GonzaloRomeroR/Teleoperation-Hexapod-Robot/Hexapod-Model/Arduino MEGA 2560 R3.jpg

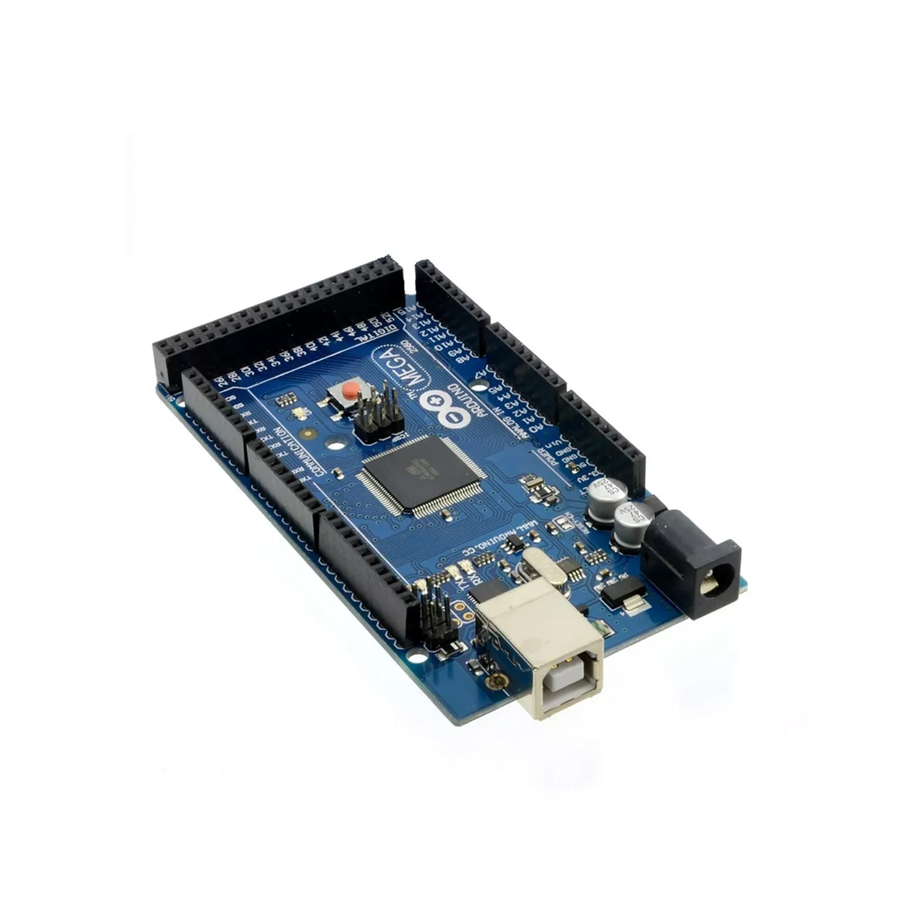
Hexapod-Model/Arduino MEGA 2560 R3.jpg
