GonzaloRomeroR/Teleoperation-Hexapod-Robot/Hexapod-Model/capture_001_10112018_191838.jpg

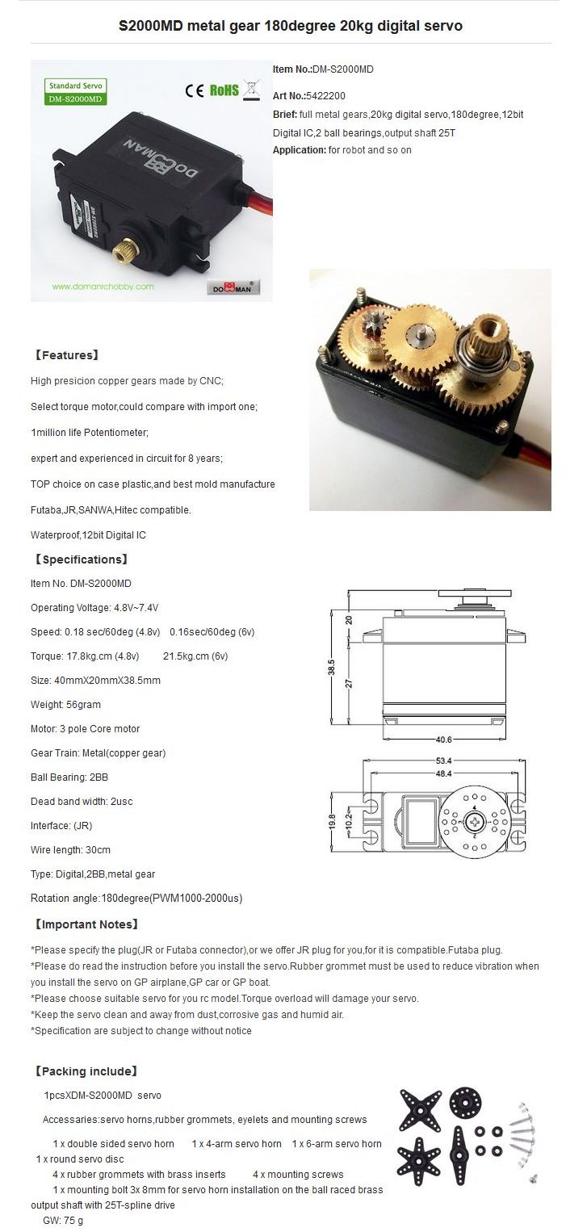
Hexapod-Model/capture_001_10112018_191838.jpg
