GonzaloRomeroR/Teleoperation-Hexapod-Robot/Hexapod-Model/DoMan Servo by Kamyar Update 1.jpg

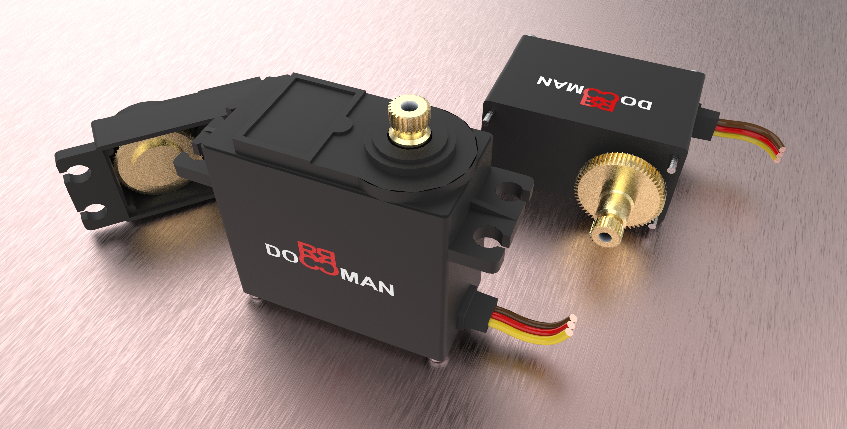
Hexapod-Model/DoMan Servo by Kamyar Update 1.jpg
