GonzaloRomeroR/Teleoperation-Hexapod-Robot/Hexapod-Model/DoMan Servo by Kamyar.jpg

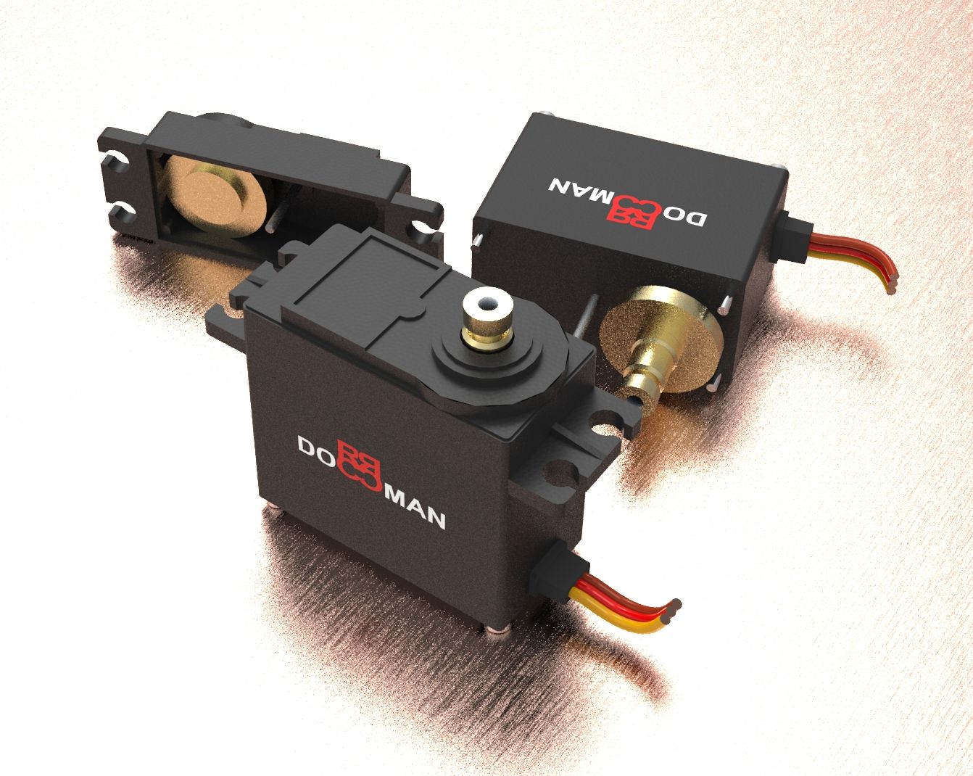
Hexapod-Model/DoMan Servo by Kamyar.jpg
