GonzaloRomeroR/Teleoperation-Hexapod-Robot/Hexapod-Model/HC-SR04.jpg

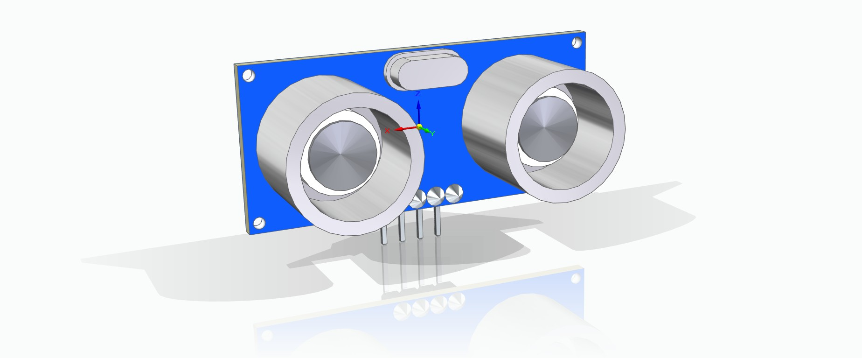
Hexapod-Model/HC-SR04.jpg
