GonzaloRomeroR/Teleoperation-Hexapod-Robot/Hexapod-Model/SensorSharpDigital/Renderings/sharp ir sensor.JPG

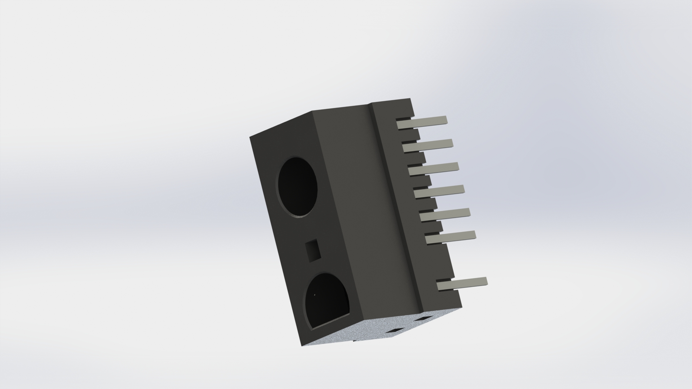
Hexapod-Model/SensorSharpDigital/Renderings/sharp ir sensor.JPG
