GonzaloRomeroR/Teleoperation-Hexapod-Robot/Hexapod-Simulation-Unity/Assets/Scripts/Joystick Pack/Sprites/All Axis Backgrounds/AllAxis_Outline.png

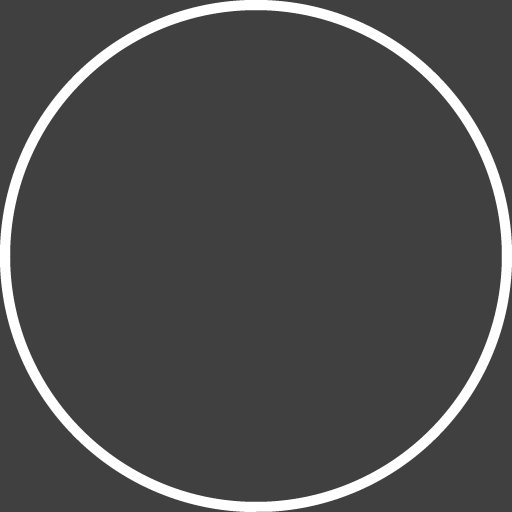
Hexapod-Simulation-Unity/Assets/Scripts/Joystick Pack/Sprites/All Axis Backgrounds/AllAxis_Outline.png
