GonzaloRomeroR/Teleoperation-Hexapod-Robot/Hexapod-Simulation-Unity/Assets/Scripts/Joystick Pack/Sprites/All Axis Backgrounds/AllAxis_Outline_Arrows.png

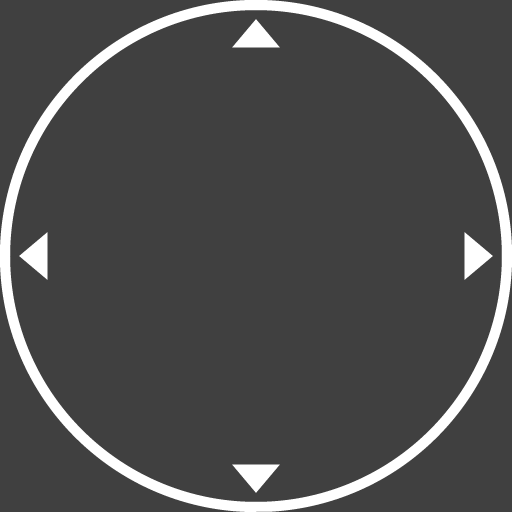
Hexapod-Simulation-Unity/Assets/Scripts/Joystick Pack/Sprites/All Axis Backgrounds/AllAxis_Outline_Arrows.png
