GonzaloRomeroR/Teleoperation-Hexapod-Robot/Hexapod-Simulation-Unity/Assets/Scripts/Joystick Pack/Sprites/All Axis Backgrounds/AllAxis_Ridged.png

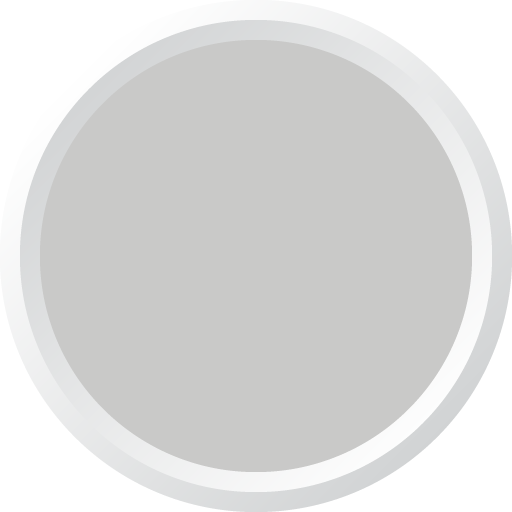
Hexapod-Simulation-Unity/Assets/Scripts/Joystick Pack/Sprites/All Axis Backgrounds/AllAxis_Ridged.png
