GonzaloRomeroR/Teleoperation-Hexapod-Robot/Hexapod-Simulation-Unity/Assets/Scripts/Joystick Pack/Sprites/All Axis Backgrounds/AllAxis_Ridged_Arrows.png

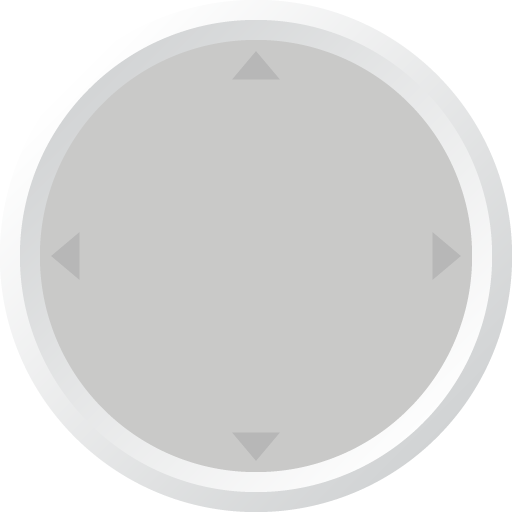
Hexapod-Simulation-Unity/Assets/Scripts/Joystick Pack/Sprites/All Axis Backgrounds/AllAxis_Ridged_Arrows.png
