GonzaloRomeroR/Teleoperation-Hexapod-Robot/Hexapod-Simulation-Unity/Assets/Scripts/Joystick Pack/Sprites/Handles/Handle_Outline_Arrows.png

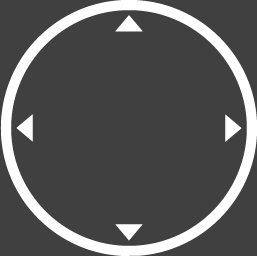
Hexapod-Simulation-Unity/Assets/Scripts/Joystick Pack/Sprites/Handles/Handle_Outline_Arrows.png
