GonzaloRomeroR/Teleoperation-Hexapod-Robot/Hexapod-Simulation-Unity/Assets/Scripts/Joystick Pack/Sprites/Handles/Handle_Ridged.png

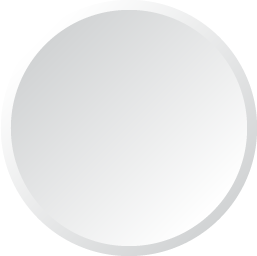
Hexapod-Simulation-Unity/Assets/Scripts/Joystick Pack/Sprites/Handles/Handle_Ridged.png
