GonzaloRomeroR/Teleoperation-Hexapod-Robot/Hexapod-Simulation-Unity/Assets/Scripts/Joystick Pack/Sprites/Horizontal Backgrounds/Horizontal_Outline.png

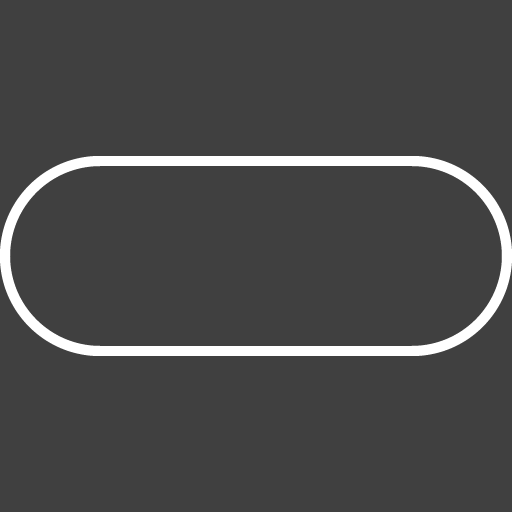
Hexapod-Simulation-Unity/Assets/Scripts/Joystick Pack/Sprites/Horizontal Backgrounds/Horizontal_Outline.png
