GonzaloRomeroR/Teleoperation-Hexapod-Robot/Hexapod-Simulation-Unity/Assets/Scripts/Joystick Pack/Sprites/Horizontal Backgrounds/Horizontal_Ridged.png

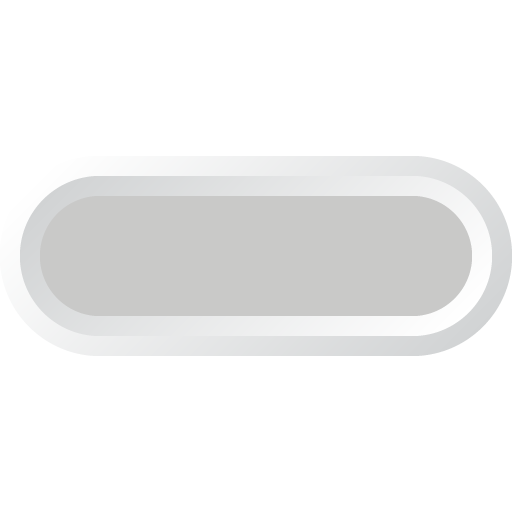
Hexapod-Simulation-Unity/Assets/Scripts/Joystick Pack/Sprites/Horizontal Backgrounds/Horizontal_Ridged.png
