GonzaloRomeroR/Teleoperation-Hexapod-Robot/Hexapod-Simulation-Unity/Assets/Scripts/Joystick Pack/Sprites/Vertical Backgrounds/Vertical_Outline_Arrows.png

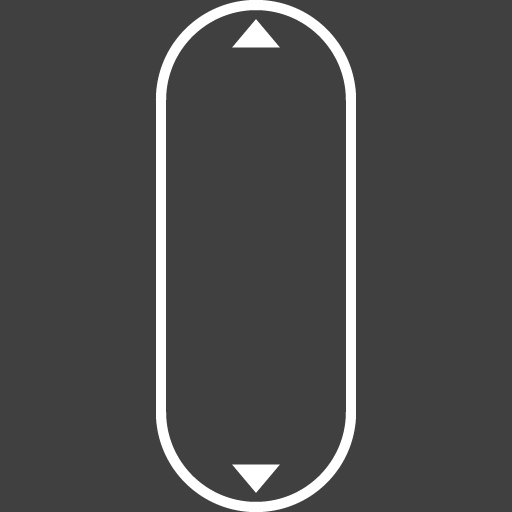
Hexapod-Simulation-Unity/Assets/Scripts/Joystick Pack/Sprites/Vertical Backgrounds/Vertical_Outline_Arrows.png
