GonzaloRomeroR/Teleoperation-Hexapod-Robot/Hexapod-Simulation-Unity/Assets/Scripts/Joystick Pack/Sprites/Vertical Backgrounds/Vertical_Plain.png

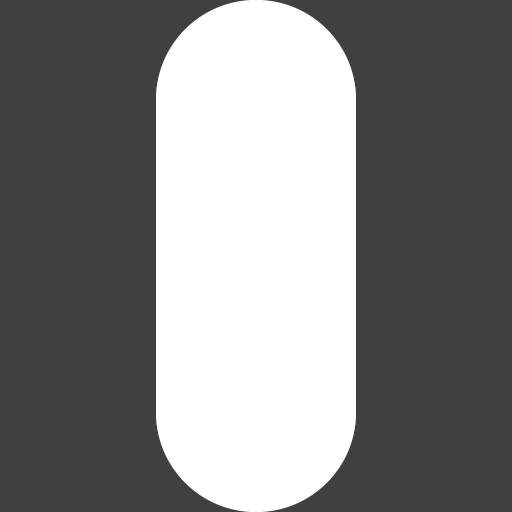
Hexapod-Simulation-Unity/Assets/Scripts/Joystick Pack/Sprites/Vertical Backgrounds/Vertical_Plain.png
