GonzaloRomeroR/Teleoperation-Hexapod-Robot/Hexapod-Simulation-Unity/Assets/Scripts/Joystick Pack/Sprites/Vertical Backgrounds/Vertical_Ridged.png

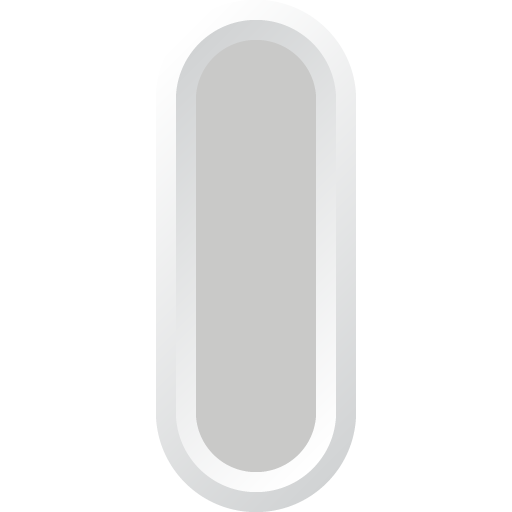
Hexapod-Simulation-Unity/Assets/Scripts/Joystick Pack/Sprites/Vertical Backgrounds/Vertical_Ridged.png
