GonzaloRomeroR/Teleoperation-Hexapod-Robot/Hexapod-Simulation-Unity/Assets/TextMesh Pro/Sprites/EmojiOne.png

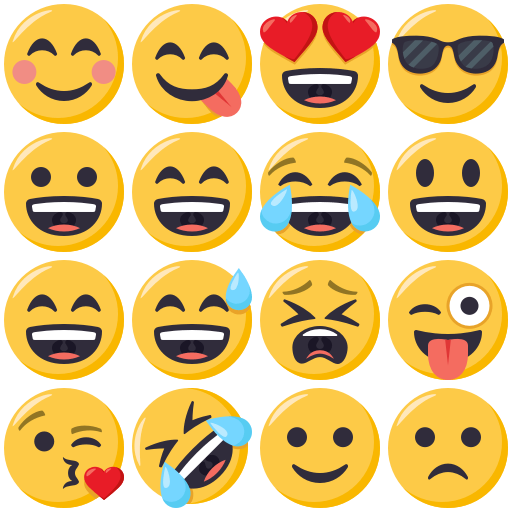
Hexapod-Simulation-Unity/Assets/TextMesh Pro/Sprites/EmojiOne.png
