GonzaloRomeroR/Teleoperation-Hexapod-Robot/Hexapod-Model/raspberry-pi-4-model-b-1.snapshot.3/VIA VL805 PCIe USB 3.0 controller, RPi4ModelB.SLDPRT

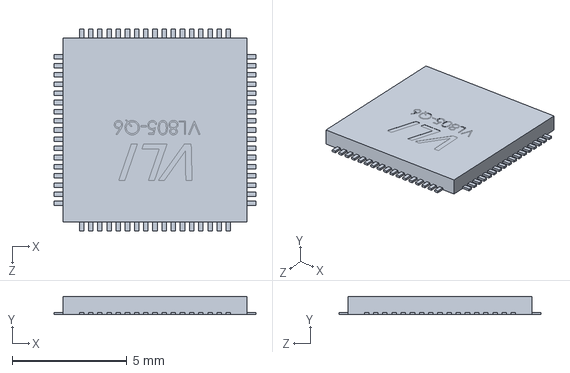
[picture p39: CAD file, 2020-07-01]
Hexapod-Model/raspberry-pi-4-model-b-1.snapshot.3/VIA VL805 PCIe USB 3.0 controller, RPi4ModelB.SLDPRT
8.80 x 0.8 x 8.80 mm
