GonzaloRomeroR/Teleoperation-Hexapod-Robot/Hexapod-Model/raspberry-pi-4-model-b-1.snapshot.3/Female USB Type C Connector, RPi4ModelB.SLDPRT

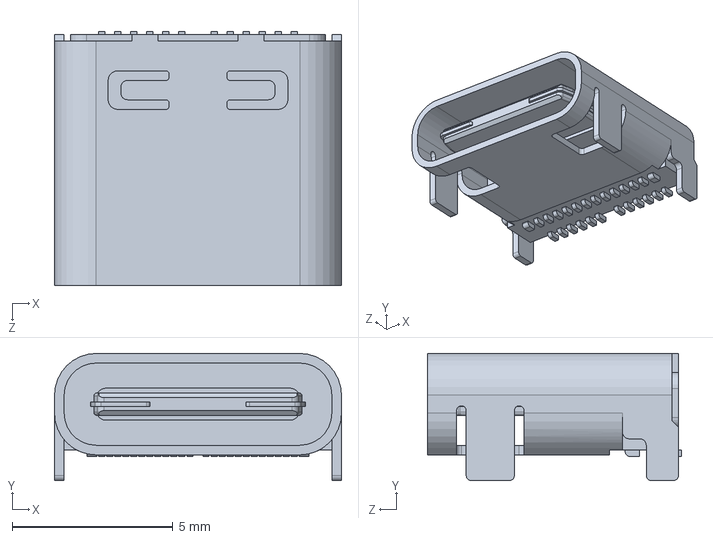
[picture p43: CAD file, 2020-07-01]
Hexapod-Model/raspberry-pi-4-model-b-1.snapshot.3/Female USB Type C Connector, RPi4ModelB.SLDPRT
8.94 x 3.96 x 7.90 mm
