GonzaloRomeroR/Teleoperation-Hexapod-Robot/Hexapod-Model/raspberry-pi-4-model-b-1.snapshot.3/Cypress CYW43455 Wireless Module Cover, RPi4ModelB.SLDPRT

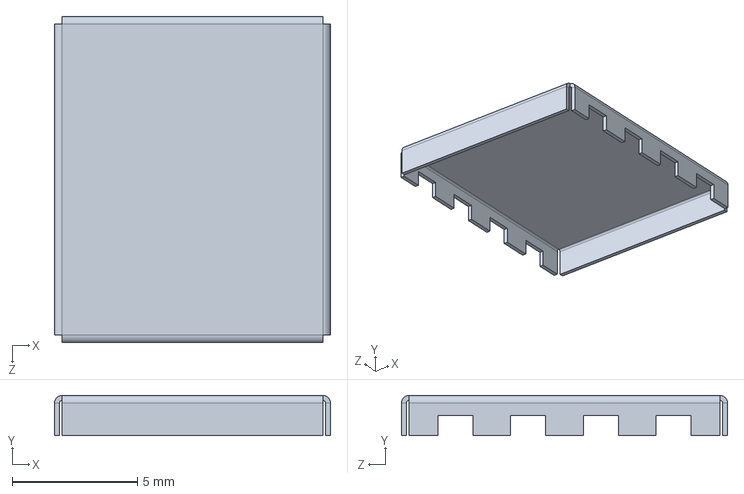
[picture p47: CAD file, 2020-07-01]
Hexapod-Model/raspberry-pi-4-model-b-1.snapshot.3/Cypress CYW43455 Wireless Module Cover, RPi4ModelB.SLDPRT
11.0 x 1.60 x 13.0 mm
