GonzaloRomeroR/Teleoperation-Hexapod-Robot/Hexapod-Model/SensorSharpDigital/PIN3Angulo.SLDPRT

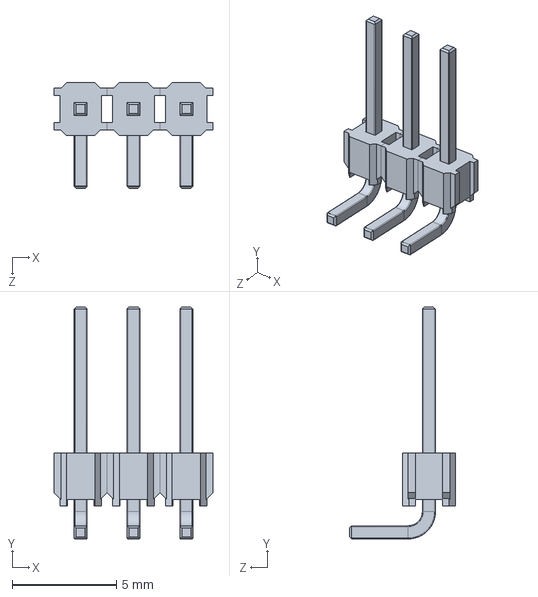
[picture p48: CAD file, 2020-07-01]
Hexapod-Model/SensorSharpDigital/PIN3Angulo.SLDPRT
7.62 x 11.1 x 5.08 mm
