GonzaloRomeroR/Teleoperation-Hexapod-Robot/Hexapod-Simulation-Unity/Assets/RobotParts/Robot1/Femur.obj

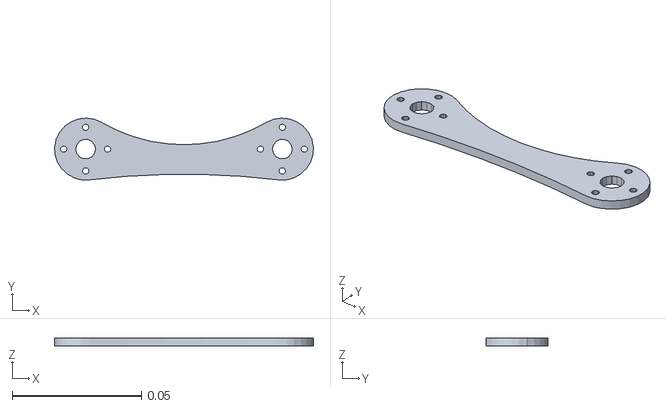
[picture p49: CAD file, 2020-04-14]
Hexapod-Simulation-Unity/Assets/RobotParts/Robot1/Femur.obj
0.1 x 0.0239 x 0.003
