GonzaloRomeroR/Teleoperation-Hexapod-Robot/Hexapod-Model/coixa1.stl

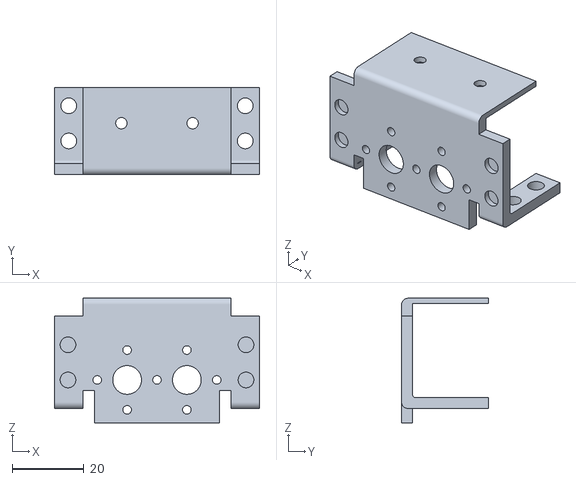
[picture p50: CAD file, 2020-07-01]
Hexapod-Model/coixa1.stl
57.2 x 24.2 x 34.7
