GonzaloRomeroR/Teleoperation-Hexapod-Robot/Hexapod-Model/raspberry-pi-4-model-b-1.snapshot.3/Broadcom BCM54213PE Gigabit Ethernet Transceiver, RPi4ModelB.SLDPRT

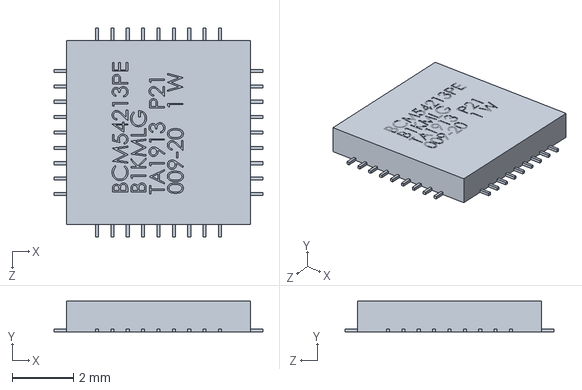
[picture p51: CAD file, 2020-07-01]
Hexapod-Model/raspberry-pi-4-model-b-1.snapshot.3/Broadcom BCM54213PE Gigabit Ethernet Transceiver, RPi4ModelB.SLDPRT
6.80 x 1.00 x 6.80 mm
