GonzaloRomeroR/Teleoperation-Hexapod-Robot/Hexapod-Model/raspberry-pi-4-model-b-1.snapshot.3/Female Micro HDMI Connector, RPi4ModelB.SLDPRT

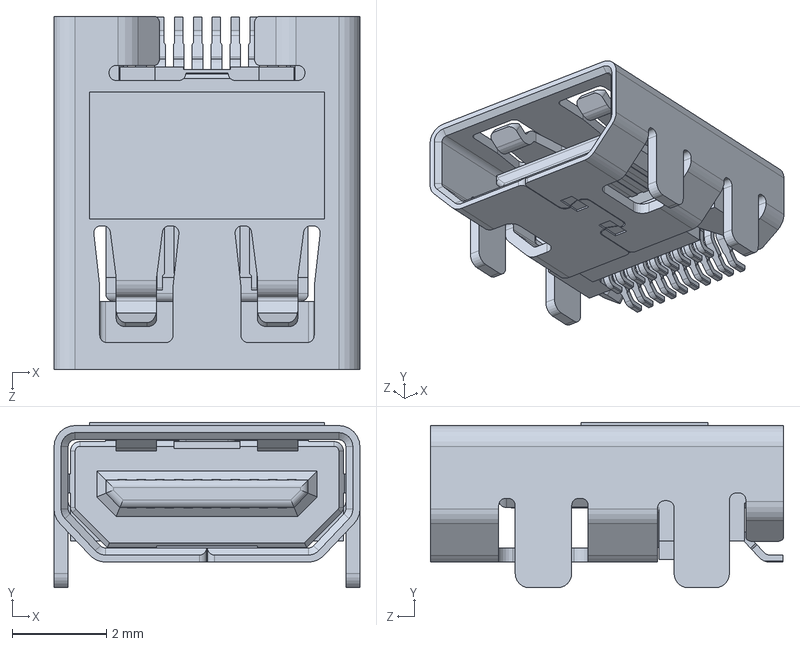
[picture p52: CAD file, 2020-07-01]
Hexapod-Model/raspberry-pi-4-model-b-1.snapshot.3/Female Micro HDMI Connector, RPi4ModelB.SLDPRT
6.50 x 3.52 x 7.50 mm
