GonzaloRomeroR/Teleoperation-Hexapod-Robot/Hexapod-Model/tibia.stl

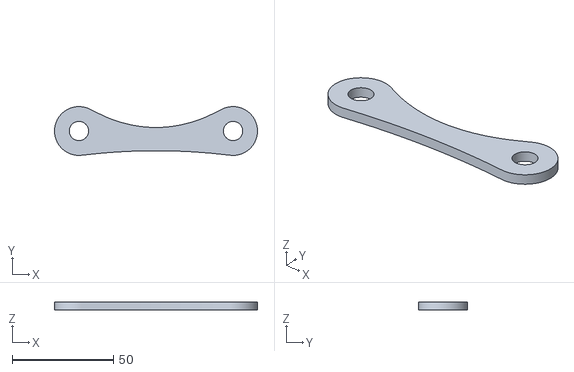
[picture p53: CAD file, 2020-07-01]
Hexapod-Model/tibia.stl
100.3 x 24.1 x 4.00
