GonzaloRomeroR/Teleoperation-Hexapod-Robot/Real-Robot-Movement/GUI.py

import math
from functools import partial
from tkinter import *

ARTICULATION_NUMBER = 18


class GUI:
    """
    Class that manage the graphical user interface of the robot.
    """

    def __init__(self, window, gl):
        """_summary_

        :param window: Tkinter window
        :type window:`Tk`
        :param gl: object with global attributes
        :type gl: `Global`
        """
        self.gl = gl
        self.lbl_joint_variables = []
        self.txt_joint_variables = []
        self.txt_platform_variables = []
        self.txt_position_variables = []
        self.art_number = 18
        self.window = window
        self.show_interface()

    def action(self, joint_number):
        row, col = self.get_list_index(joint_number)
        value = self.txt_joint_variables[joint_number].get()
        self.gl.set_joint_trajectory([float(value)], [1.0], row, col)

    def platform_action(self, plat_var_number):
        value = self.txt_platform_variables[plat_var_number].get()
        self.gl.platform_variables[plat_var_number] = float(value)
        self.gl.platform_movement()

    def walking_action(self):
        value = self.txt_walk.get()
        self.gl.walking_input(float(value) * math.pi / 180)

    def rotation_action(self, direction):
        # value = self.txt_walk.get()
        self.gl.rotation_input(direction)
        pass

    def move_action(self):
        X = self.txt_position_variables[0].get()
        Y = self.txt_position_variables[1].get()
        self.gl.set_robot_movement(int(X), int(Y))

    def rotation_step_action(self):
        value = int(self.txt_rotation_step.get())
        self.gl.set_rotation_step(value)

    def step_height_action(self):
        value = int(self.txt_step_height.get())
        self.gl.set_step_height(value)

    def step_distance_action(self):
        value = int(self.txt_step_distance.get())
        self.gl.set_step_distance(value)

    def velocity_action(self):
        value = float(self.txt_velocity.get())
        self.gl.set_velocity(value)

    def show_interface(self):
        row_number = 0
        row_number = self.create_platform_inputs(row_number)
        row_number = self.create_joints_titles(row_number)
        row_number = self.create_joints_inputs(row_number)
        row_number = self.create_walking_input(row_number)
        row_number = self.create_rotation_input(row_number)
        row_number = self.create_position_input(row_number)
        row_number = self.create_parameters_inputs(row_number)

    def create_position_input(self, row_number):
        lbl_rot = Label(self.window, text="Position", font=("Arial Bold", 15))
        lbl_rot.grid(sticky="W", column=0, row=row_number)
        row_number = row_number + 1

        lbl_x = Label(self.window, text="X", font=("Arial", 12))
        lbl_x.grid(column=1, row=row_number)

        lbl_y = Label(self.window, text="Y", font=("Arial", 12))
        lbl_y.grid(column=2, row=row_number)
        row_number = row_number + 1

        counter_column = 1
        for i in range(2):
            self.txt_position_variables.append(Entry(self.window, width=10))
            self.txt_position_variables[i].grid(column=counter_column, row=row_number)
            counter_column = counter_column + 1

        btn = Button(self.window, text="Move", command=self.move_action)
        btn.grid(column=counter_column, row=row_number)
        row_number = row_number + 1

        return row_number

    def create_rotation_input(self, row_number):
        lbl_rot = Label(self.window, text="Rotation", font=("Arial Bold", 15))
        lbl_rot.grid(sticky="W", column=0, row=row_number)
        row_number = row_number + 1

        btn = Button(self.window, text="C", command=partial(self.rotation_action, True))
        btn.grid(column=1, row=row_number)

        btn = Button(
            self.window, text="CC", command=partial(self.rotation_action, False)
        )
        btn.grid(column=2, row=row_number)

        row_number = row_number + 1
        return row_number

    def create_walking_input(self, row_number):
        lbl_walk = Label(self.window, text="Walk", font=("Arial Bold", 15))
        lbl_walk.grid(sticky="W", column=0, row=row_number)
        row_number = row_number + 1

        btn = Button(self.window, text="Walk", command=self.walking_action)
        btn.grid(column=1, row=row_number)

        self.txt_walk = Entry(self.window, width=10)
        self.txt_walk.grid(column=2, row=row_number)

        row_number = row_number + 1
        return row_number

    def create_platform_inputs(self, row_number):
        lbl_platform = Label(self.window, text="Platform", font=("Arial Bold", 15))
        lbl_platform.grid(sticky="W", column=0, row=row_number)
        row_number = row_number + 1

        lbl_x = Label(self.window, text="X", font=("Arial", 12))
        lbl_x.grid(column=1, row=row_number)

        lbl_y = Label(self.window, text="Y", font=("Arial", 12))
        lbl_y.grid(column=3, row=row_number)

        lbl_z = Label(self.window, text="Z", font=("Arial", 12))
        lbl_z.grid(column=5, row=row_number)
        row_number = row_number + 1

        counter_column = 1
        for i in range(3):

            self.txt_platform_variables.append(Entry(self.window, width=10))
            self.txt_platform_variables[i].grid(column=counter_column, row=row_number)
            counter_column = counter_column + 1

            btn = Button(
                self.window, text="Update", command=partial(self.platform_action, i)
            )
            btn.grid(column=counter_column, row=row_number)
            counter_column = counter_column + 1
        row_number = row_number + 1

        lbl_x = Label(self.window, text="Roll", font=("Arial", 12))
        lbl_x.grid(column=1, row=row_number)

        lbl_y = Label(self.window, text="Pitch", font=("Arial", 12))
        lbl_y.grid(column=3, row=row_number)

        lbl_z = Label(self.window, text="Yaw", font=("Arial", 12))
        lbl_z.grid(column=5, row=row_number)
        row_number = row_number + 1

        counter_column = 1
        for i in range(3):

            self.txt_platform_variables.append(Entry(self.window, width=10))
            self.txt_platform_variables[i + 3].grid(
                column=counter_column, row=row_number
            )
            counter_column = counter_column + 1

            btn = Button(
                self.window, text="Update", command=partial(self.platform_action, i + 3)
            )
            btn.grid(column=counter_column, row=row_number)
            counter_column = counter_column + 1
        row_number = row_number + 1
        return row_number

    def create_parameters_inputs(self, row_number):
        lbl_platform = Label(self.window, text="Parameters", font=("Arial Bold", 15))
        lbl_platform.grid(sticky="W", column=0, row=row_number)
        row_number = row_number + 1

        lbl_x = Label(self.window, text="Vel(1[])", font=("Arial", 12))
        lbl_x.grid(column=1, row=row_number)

        lbl_z = Label(self.window, text="S_D(120[mm])", font=("Arial", 12))
        lbl_z.grid(column=3, row=row_number)
        row_number = row_number + 1

        counter_column = 1

        self.txt_velocity = Entry(self.window, width=10)
        self.txt_velocity.grid(column=counter_column, row=row_number)
        counter_column = counter_column + 1

        btn = Button(self.window, text="Update", command=self.velocity_action)
        btn.grid(column=counter_column, row=row_number)
        counter_column = counter_column + 1

        self.txt_step_distance = Entry(self.window, width=10)
        self.txt_step_distance.grid(column=counter_column, row=row_number)
        counter_column = counter_column + 1

        btn = Button(self.window, text="Update", command=self.step_distance_action)
        btn.grid(column=counter_column, row=row_number)
        counter_column = counter_column + 1

        row_number = row_number + 1

        lbl_x = Label(self.window, text="S_H(60[mm])", font=("Arial", 12))
        lbl_x.grid(column=1, row=row_number)

        lbl_y = Label(self.window, text="R_S(20[°])", font=("Arial", 12))
        lbl_y.grid(column=3, row=row_number)

        row_number = row_number + 1

        counter_column = 1

        self.txt_step_height = Entry(self.window, width=10)
        self.txt_step_height.grid(column=counter_column, row=row_number)
        counter_column = counter_column + 1

        btn = Button(self.window, text="Update", command=self.step_height_action)
        btn.grid(column=counter_column, row=row_number)
        counter_column = counter_column + 1

        self.txt_rotation_step = Entry(self.window, width=10)
        self.txt_rotation_step.grid(column=counter_column, row=row_number)
        counter_column = counter_column + 1

        btn = Button(self.window, text="Update", command=self.rotation_step_action)
        btn.grid(column=counter_column, row=row_number)
        counter_column = counter_column + 1

        row_number = row_number + 1
        return row_number

    def create_joints_titles(self, row_number):
        lbl_joints = Label(self.window, text="Joints", font=("Arial Bold", 15))
        lbl_joints.grid(sticky="W", column=0, row=row_number)
        row_number = row_number + 1

        lbl_coxa = Label(self.window, text="Coxa", font=("Arial", 12))
        lbl_coxa.grid(column=1, row=row_number)

        lbl_femur = Label(self.window, text="Femur", font=("Arial", 12))
        lbl_femur.grid(column=3, row=row_number)

        lbl_tibia = Label(self.window, text="Tibia", font=("Arial", 12))
        lbl_tibia.grid(column=5, row=row_number)
        row_number = row_number + 1
        return row_number

    def get_list_index(self, joint_number):
        counter_row = 0
        counter_column = 0
        for i in range(ARTICULATION_NUMBER):
            if joint_number == i:
                return counter_row, counter_column
            counter_column = counter_column + 1
            if counter_column == 3:
                counter_column = 0
                counter_row = counter_row + 1

    def create_joints_inputs(self, row_number):
        counter_row = 0
        counter_column = 1

        for i in range(self.art_number):
            self.txt_joint_variables.append(Entry(self.window, width=10))
            self.txt_joint_variables[i].grid(
                column=counter_column, row=row_number + counter_row
            )
            counter_column = counter_column + 1

            btn = Button(self.window, text="Update", command=partial(self.action, i))
            btn.grid(column=counter_column, row=row_number + counter_row)
            counter_column = counter_column + 1

            if counter_column > 6:
                counter_column = 1
                counter_row = counter_row + 1

                self.lbl_joint_variables.append(
                    Label(self.window, text=str(counter_row), font=("Arial", 12))
                )
                self.lbl_joint_variables[counter_row - 1].grid(
                    column=0, row=row_number + counter_row - 1
                )

        return row_number + counter_row


def runGUI(gl):
    """
    Run GUI

    :param gl: object with global variables
    :type gl: `Global`
    """
    window = Tk()
    window.title("Hexapod View")
    GUI(window, gl)
    window.geometry("700x700")
    window.mainloop()
